DanNixon/Dilbert/firmware/src/DebugApp.h

/*! @file */

#pragma once

#include <App.h>

/**
 * @class DebugApp
 * @author Dan Nixon
 * @brief App containing debug information and button test.
 */
class DebugApp : public App
{
public:
  DebugApp();
  virtual ~DebugApp();

  virtual void onEntry();
  virtual bool handleButton(IButton *button);
};
